JKN0/RocManV2/Software/graphdata.h

/***************************************************************************

 graphdata.h
 
 RocMan - PacMan for junk led matrix

 Controller: STC8A8K64D4 @ breakout
 
 12.12.2024  - First version

 ***************************************************************************/

// Maze bitmap
// 8 pixels/byte
BYTE CODE maze[88][11] = {
    { 0x00,0x00,0x00,0x00,0x00,0x00,0x00,0x00,0x00,0x00,0x00 },
    { 0x00,0x00,0x00,0x00,0x00,0x00,0x00,0x00,0x00,0x00,0x00 },
    { 0x00,0x00,0x00,0x00,0x00,0x00,0x00,0x00,0x00,0x00,0x00 },
    { 0x00,0x00,0x00,0x00,0x00,0x00,0x00,0x00,0x00,0x00,0x00 },
    { 0x00,0x00,0x00,0x00,0x00,0x00,0x00,0x00,0x00,0x00,0x00 },
    { 0x00,0x00,0x00,0x00,0x00,0x00,0x00,0x00,0x00,0x00,0x00 },
    { 0x00,0x00,0x00,0x00,0x00,0x00,0x00,0x00,0x00,0x00,0x00 },
    { 0x07,0xFF,0xFF,0xFF,0xFC,0x0F,0xFF,0xFF,0xFF,0xF8,0x00 },
    { 0x08,0x00,0x00,0x00,0x02,0x10,0x00,0x00,0x00,0x04,0x00 },
    { 0x10,0x00,0x00,0x00,0x01,0x20,0x00,0x00,0x00,0x02,0x00 },
    { 0x10,0x00,0x00,0x00,0x01,0x20,0x00,0x00,0x00,0x02,0x00 },
    { 0x10,0x00,0x00,0x00,0x01,0x20,0x00,0x00,0x00,0x02,0x00 },
    { 0x10,0x00,0x00,0x00,0x01,0x20,0x00,0x00,0x00,0x02,0x00 },
    { 0x10,0x3E,0x03,0xFF,0x81,0x20,0x7F,0xF0,0x1F,0x02,0x00 },
    { 0x10,0x41,0x04,0x00,0x41,0x20,0x80,0x08,0x20,0x82,0x00 },
    { 0x10,0x41,0x04,0x00,0x41,0x20,0x80,0x08,0x20,0x82,0x00 },
    { 0x10,0x3E,0x03,0xFF,0x80,0xC0,0x7F,0xF0,0x1F,0x02,0x00 },
    { 0x10,0x00,0x00,0x00,0x00,0x00,0x00,0x00,0x00,0x02,0x00 },
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
    { 0,C,C,C,0 },
    { C,C,C,C,C },
    { C,E,C,E,C },
    { C,C,C,C,C },
    { C,0,C,0,C }
};

BYTE CODE ghost_blue_b[5][5] = {
    { 0,C,C,C,0 },
    { C,C,C,C,C },
    { C,E,C,E,C },
    { C,C,C,C,C },
    { 0,C,0,C,0 }
};

#undef  C
#undef  E
#define C 2
#define E 3

// white (flashing) ghost does not need b-animation, because it is 
// alternated with blue_b
BYTE CODE ghost_white_a[5][5] = {
    { 0,C,C,C,0 },
    { C,C,C,C,C },
    { C,E,C,E,C },
    { C,C,C,C,C },
    { C,0,C,0,C }
};

#undef  E
#define E 2

BYTE CODE ghost_eyes[5][5] = {
    { 0,0,0,0,0 },
    { 0,E,0,E,0 },
    { 0,0,0,0,0 },
    { 0,0,0,0,0 },
    { 0,0,0,0,0 }
};

// --- Points (1...4) after ghost eaten

#undef  C
#define C 3

BYTE CODE ghost_explosion_1[5][5] = {
    { 0,0,C,0,0 },
    { 0,C,C,0,0 },
    { 0,0,C,0,0 },
    { 0,0,C,0,0 },
    { 0,C,C,C,0 }
};

BYTE CODE ghost_explosion_2[5][5] = {
    { 0,0,C,C,0 },
    { 0,C,0,0,C },
    { 0,0,0,C,0 },
    { 0,0,C,0,0 },
    { 0,C,C,C,C }
};

BYTE CODE ghost_explosion_3[5][5] = {
    { 0,C,C,C,C },
    { 0,0,0,0,C },
    { 0,0,0,C,0 },
    { 0,C,0,0,C },
    { 0,0,C,C,0 }
};

BYTE CODE ghost_explosion_4[5][5] = {
    { 0,C,0,0,C },
    { 0,C,0,0,C },
    { 0,C,C,C,C },
    { 0,0,0,0,C },
    { 0,0,0,0,C }
};

// --- Fruits

#define B 9
#define R 3
#define P 14
#define G 4
#define Y 15

BYTE CODE fruit0[5][5] = {
    { 0,0,0,0,B },
    { 0,0,0,B,0 },
    { 0,B,B,B,0 },
    { R,R,0,R,R },
    { P,R,0,P,R }
};

BYTE CODE fruit1[5][5] = {
    { 0,G,G,G,0 },
    { R,R,G,R,R },
    { R,Y,R,R,R },
    { R,R,R,Y,R },
    { 0,R,R,R,0 }
};

BYTE CODE fruit2[5][5] = {
    { 0,0,G,G,G },
    { 0,Y,Y,Y,0 },
    { Y,Y,Y,Y,Y },
    { Y,Y,Y,Y,Y },
    { 0,Y,Y,Y,0 }
};

#undef B
#undef R
#undef P
#undef G
#undef Y
#undef C
#undef E
