JKN0/RocManV2/Software/soundata.h

/***************************************************************************

 soundata.h

 RocMan - PacMan for junk led matrix
 
 Controller: STC8A8K64D4 @ breakout
 
 8.1.2025  - First version

 ***************************************************************************/

/* ---------------------  Note values  ------------------------- */

#define NOTE_D6            (WORD)(-1596)    // D6 
#define NOTE_C6H           (WORD)(-1691)    // C#6/Db6 
#define NOTE_C6            (WORD)(-1792)    // C6
#define NOTE_B5            (WORD)(-1898)    // B5 
#define NOTE_A5H           (WORD)(-2011)    // A#5/Bb5 
#define NOTE_A5            (WORD)(-2131)    // A5 
#define NOTE_G5H           (WORD)(-2257)    // G#5/Ab5 
#define NOTE_G5            (WORD)(-2392)    // G5 
#define NOTE_F5H           (WORD)(-2534)    // F#5/Gb5 
#define NOTE_F5            (WORD)(-2684)    // F5 
#define NOTE_E5            (WORD)(-2844)    // E5 
#define NOTE_D5H           (WORD)(-3013)    // D#5/Eb5 
#define NOTE_D5            (WORD)(-3192)    // D5 
#define NOTE_C5H           (WORD)(-3382)    // C#5/Db5 
#define NOTE_C5            (WORD)(-3583)    // C5
#define NOTE_B4            (WORD)(-3796)    // B4 
#define NOTE_A4H           (WORD)(-4022)    // A#4/Bb4 
#define NOTE_A4            (WORD)(-4261)    // A4 A440 
#define NOTE_G4H           (WORD)(-4515)    // G#4/Ab4 
#define NOTE_G4            (WORD)(-4783)    // G4 
#define NOTE_F4H           (WORD)(-5068)    // F#4/Gb4 
#define NOTE_F4            (WORD)(-5369)    // F4 
#define NOTE_E4            (WORD)(-5688)    // E4 
#define NOTE_D4H           (WORD)(-6026)    // D#4/Eb4 
#define NOTE_D4            (WORD)(-6385)    // D4 
#define NOTE_C4H           (WORD)(-6764)    // C#4/Db4 
#define NOTE_C4            (WORD)(-7167)    // C4 -- Middle C 
#define NOTE_B3            (WORD)(-7593)    // B3 
#define NOTE_A3H           (WORD)(-8044)    // A#3/Bb3 
#define NOTE_A3            (WORD)(-8523)    // A3 
#define NOTE_G3H           (WORD)(-9030)    // G#3/Ab3 
#define NOTE_G3            (WORD)(-9566)    // G3 
#define NOTE_F3H           (WORD)(-10135)   // F#3/Gb3 
#define NOTE_F3            (WORD)(-10738)   // F3 

// Durations at 250 BPM
#define DUR_QUARTER        23               // 1/4 note 240 ms
#define DUR_EIGHTH_DOT     17               // dotted 1/8 note 180 ms
#define DUR_EIGHTH         11               // 1/8 note 120 ms
#define DUR_SIXTEENTH      5                // 1/16 note 60 ms
#define DUR_SIXT_TRIPLET   3                // 1/16 triplet note 40 ms

/* ---------------------  Sound sequences  ------------------------- */

SOUND_SEQ_T CODE seq_ready_jingle1[] = {
    { NOTE_C5,  DUR_SIXTEENTH,    FALSE },
    { PAUSE,    DUR_SIXTEENTH,    FALSE },
    { NOTE_C6,  DUR_EIGHTH,       FALSE },
    { NOTE_G5,  DUR_EIGHTH,       FALSE },
    { NOTE_E5,  DUR_EIGHTH,       FALSE },
    { NOTE_C6,  DUR_SIXTEENTH,    FALSE },
    { NOTE_G5,  DUR_SIXTEENTH,    FALSE }, 
    { PAUSE,    DUR_EIGHTH,       FALSE },
    { NOTE_E5,  DUR_EIGHTH,       FALSE },
    { PAUSE,    DUR_EIGHTH,       FALSE },

    { NOTE_C5H, DUR_SIXTEENTH,    FALSE },
    { PAUSE,    DUR_SIXTEENTH,    FALSE },
    { NOTE_C6H, DUR_EIGHTH,       FALSE },
    { NOTE_G5H, DUR_EIGHTH,       FALSE },
    { NOTE_F5,  DUR_EIGHTH,       FALSE },
    { NOTE_C6H, DUR_SIXTEENTH,    FALSE },
    { NOTE_G5H, DUR_SIXTEENTH,    FALSE },
    { PAUSE,    DUR_EIGHTH,       FALSE },
    { NOTE_F5,  DUR_EIGHTH,       FALSE },
    { PAUSE,    DUR_EIGHTH,       FALSE },

    { NOTE_C5,  DUR_SIXTEENTH,    FALSE },
    { PAUSE,    DUR_SIXTEENTH,    FALSE },
    { NOTE_C6,  DUR_EIGHTH,       FALSE },
    { NOTE_G5,  DUR_EIGHTH,       FALSE },
    { NOTE_E5,  DUR_EIGHTH,       FALSE },
    { NOTE_G5,  DUR_EIGHTH,       FALSE },
    { PAUSE,    DUR_EIGHTH,       FALSE },
    { NOTE_E5,  DUR_EIGHTH,       FALSE },
    { PAUSE,    DUR_EIGHTH,       FALSE },
    
    { NOTE_D5,  DUR_SIXT_TRIPLET, FALSE },
    { NOTE_D5H, DUR_SIXT_TRIPLET, FALSE },
    { NOTE_E5,  DUR_SIXT_TRIPLET, FALSE },
    { PAUSE,    DUR_EIGHTH,       FALSE },
    { NOTE_E5,  DUR_SIXT_TRIPLET, FALSE },
    { NOTE_F5,  DUR_SIXT_TRIPLET, FALSE },
    { NOTE_F5H, DUR_SIXT_TRIPLET, FALSE },
    { PAUSE,    DUR_EIGHTH,       FALSE },
    { NOTE_F5,  DUR_SIXT_TRIPLET, FALSE },
    { NOTE_F5H, DUR_SIXT_TRIPLET, FALSE },
    { NOTE_G5,  DUR_SIXT_TRIPLET, FALSE },
    { PAUSE,    DUR_EIGHTH,       FALSE },
    { NOTE_C6,  DUR_QUARTER,      FALSE },

    { EOS }
};

SOUND_SEQ_T CODE seq_ready_jingle2[] = {
    { NOTE_G4,  DUR_EIGHTH,       FALSE },
    { PAUSE,    DUR_QUARTER,      FALSE },
    { NOTE_G4,  DUR_EIGHTH,       FALSE },
    { NOTE_C4,  DUR_EIGHTH,       FALSE },
    { PAUSE,    DUR_EIGHTH,       FALSE },
    { NOTE_G4,  DUR_QUARTER,      FALSE },

    { NOTE_G4H, DUR_EIGHTH,       FALSE },
    { PAUSE,    DUR_QUARTER,      FALSE },
    { NOTE_G4H, DUR_EIGHTH,       FALSE },
    { NOTE_C4H, DUR_EIGHTH,       FALSE },
    { PAUSE,    DUR_EIGHTH,       FALSE },
    { NOTE_G4H, DUR_QUARTER,      FALSE },

    { NOTE_G4,  DUR_EIGHTH,       FALSE },
    { PAUSE,    DUR_QUARTER,      FALSE },
    { NOTE_G4,  DUR_EIGHTH,       FALSE },
    { NOTE_C4,  DUR_EIGHTH,       FALSE },
    { PAUSE,    DUR_EIGHTH,       FALSE },
    { NOTE_G4,  DUR_QUARTER,      FALSE },

    { NOTE_G4,  DUR_EIGHTH_DOT,   FALSE },
    { PAUSE,    DUR_SIXTEENTH,    FALSE },
    { NOTE_A4,  DUR_EIGHTH_DOT,   FALSE },
    { PAUSE,    DUR_SIXTEENTH,    FALSE },
    { NOTE_B4,  DUR_EIGHTH_DOT,   FALSE },
    { PAUSE,    DUR_SIXTEENTH,    FALSE },
    { NOTE_C5,  DUR_QUARTER,      FALSE },

    { EOS }
};

// Normal backing sound
SOUND_SEQ_T CODE seq_run_a[] = {
    { (WORD)(-2678), 0, TRUE  },    // 700 Hz
    { (WORD)(-2741), 0, TRUE  },    // 684 Hz
    { (WORD)(-2806), 0, TRUE  },    // 668 Hz
    { (WORD)(-2875), 0, TRUE  },    // 652 Hz
    { (WORD)(-2948), 0, TRUE  },    // 636 Hz
    { (WORD)(-3024), 0, TRUE  },    // 620 Hz
    { (WORD)(-3104), 0, TRUE  },    // 604 Hz
    { (WORD)(-3188), 0, TRUE  },    // 588 Hz
    { (WORD)(-3277), 0, TRUE  },    // 572 Hz
    { (WORD)(-3372), 0, TRUE  },    // 556 Hz
    { (WORD)(-3472), 0, TRUE  },    // 540 Hz
    { (WORD)(-3578), 0, TRUE  },    // 524 Hz
    { (WORD)(-3690), 0, TRUE  },    // 508 Hz
    { (WORD)(-3810), 0, TRUE  },    // 492 Hz
    { (WORD)(-3939), 0, TRUE  },    // 476 Hz
    { (WORD)(-4076), 0, TRUE  },    // 460 Hz
    { (WORD)(-4222), 0, TRUE  },    // 444 Hz
    { (WORD)(-4380), 0, TRUE  },    // 428 Hz
    { (WORD)(-4550), 0, TRUE  },    // 412 Hz

    { (WORD)(-4687), 0, TRUE  },    // 400 Hz
    { (WORD)(-4507), 0, TRUE  },    // 416 Hz
    { (WORD)(-4340), 0, TRUE  },    // 432 Hz
    { (WORD)(-4185), 0, TRUE  },    // 448 Hz
    { (WORD)(-4040), 0, TRUE  },    // 464 Hz
    { (WORD)(-3906), 0, TRUE  },    // 480 Hz
    { (WORD)(-3780), 0, TRUE  },    // 496 Hz
    { (WORD)(-3662), 0, TRUE  },    // 512 Hz
    { (WORD)(-3551), 0, TRUE  },    // 528 Hz
    { (WORD)(-3446), 0, TRUE  },    // 544 Hz
    { (WORD)(-3348), 0, TRUE  },    // 560 Hz
    { (WORD)(-3255), 0, TRUE  },    // 576 Hz
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
    { (WORD)(-5151), 1, TRUE  },    // 364 Hz
    { (WORD)(-5067), 1, TRUE  },    // 370 Hz
    { (WORD)(-4986), 1, TRUE  },    // 376 Hz
    { (WORD)(-4908), 1, TRUE  },    // 382 Hz
    { (WORD)(-4832), 1, TRUE  },    // 388 Hz
    { (WORD)(-4758), 1, TRUE  },    // 394 Hz

    { EOS }
};
